tekdemo/tiny-tiny-isp/gerbers/tiny-tinyisp.topsoldermask.ger.png

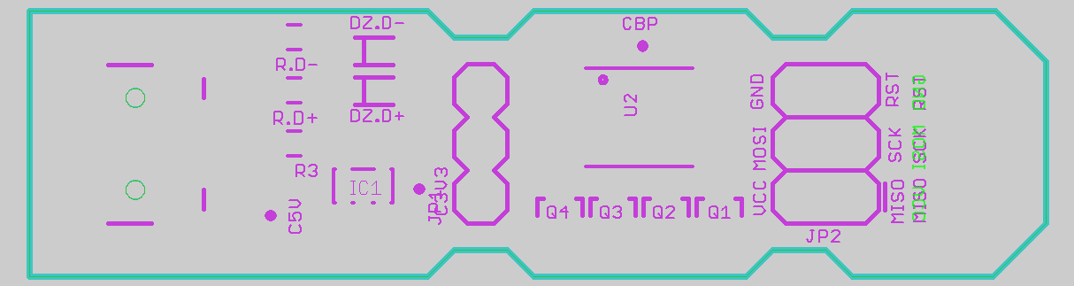
gerbers/tiny-tinyisp.topsoldermask.ger.png
